AndresRicoM/MAIA/images/light_module.png

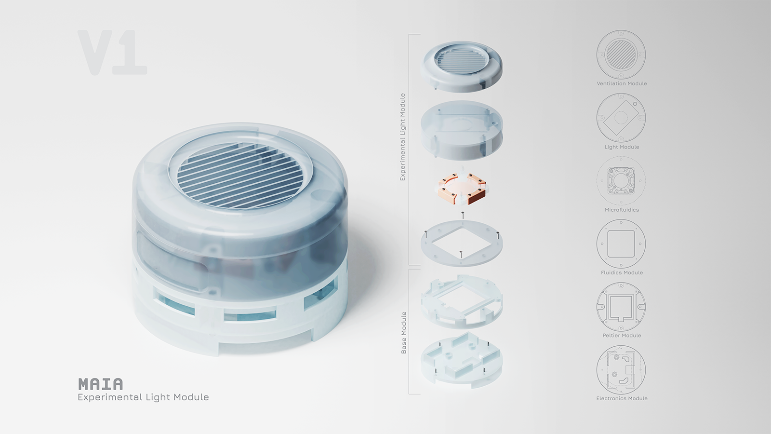
images/light_module.png
