AndresRicoM/MAIA/images/MAIA.gif

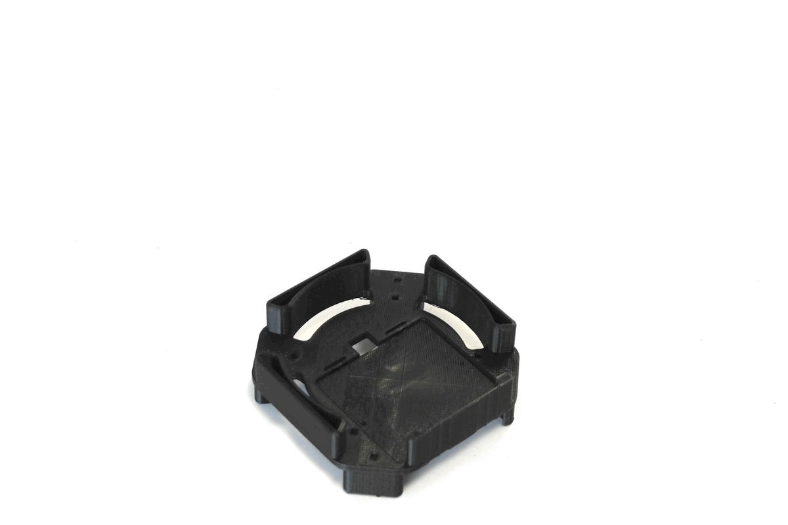
images/MAIA.gif
