AndresRicoM/MAIA/images/reactor.jpeg

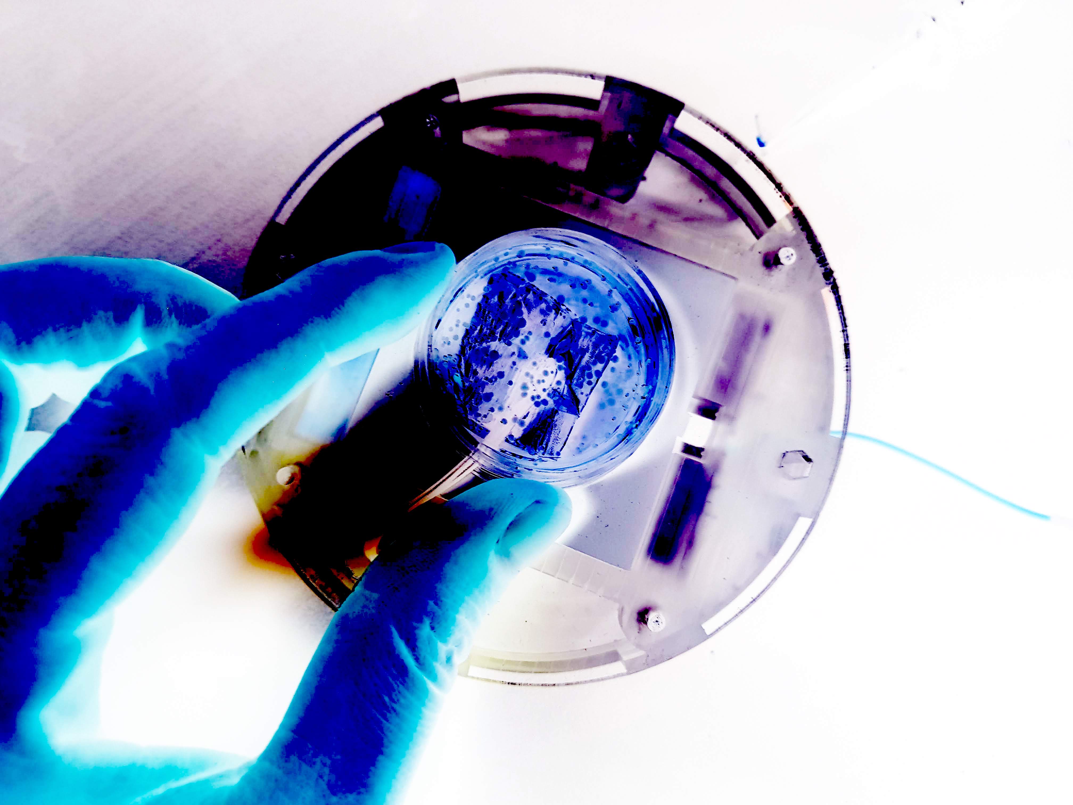
images/reactor.jpeg
