AndresRicoM/MAIA/simple_power_module/milling_files/maia_simple_power_traces.png

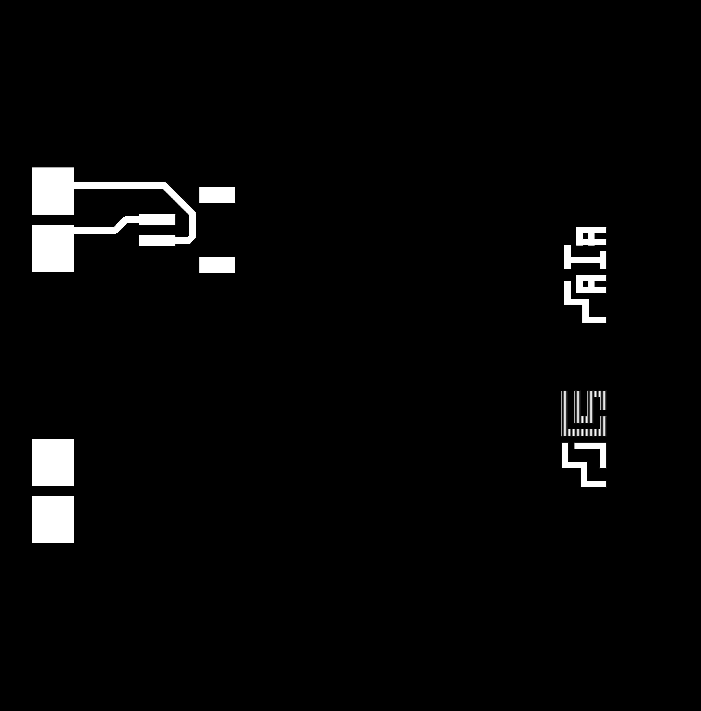
simple_power_module/milling_files/maia_simple_power_traces.png
