AndresRicoM/MAIA/light_module/pcb_fabrication/milling_files/maia_light_outline_out.png

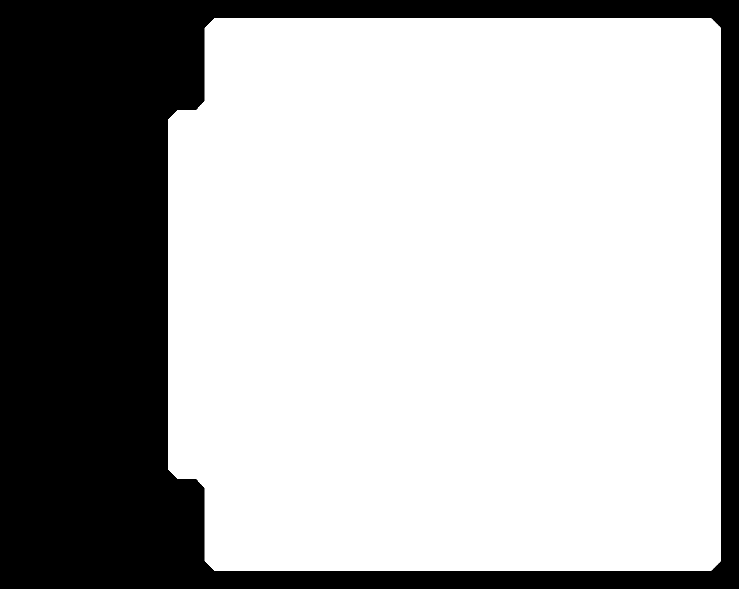
light_module/pcb_fabrication/milling_files/maia_light_outline_out.png
