AndresRicoM/MAIA/light_module/pcb_fabrication/milling_files/maia_light_traces.png

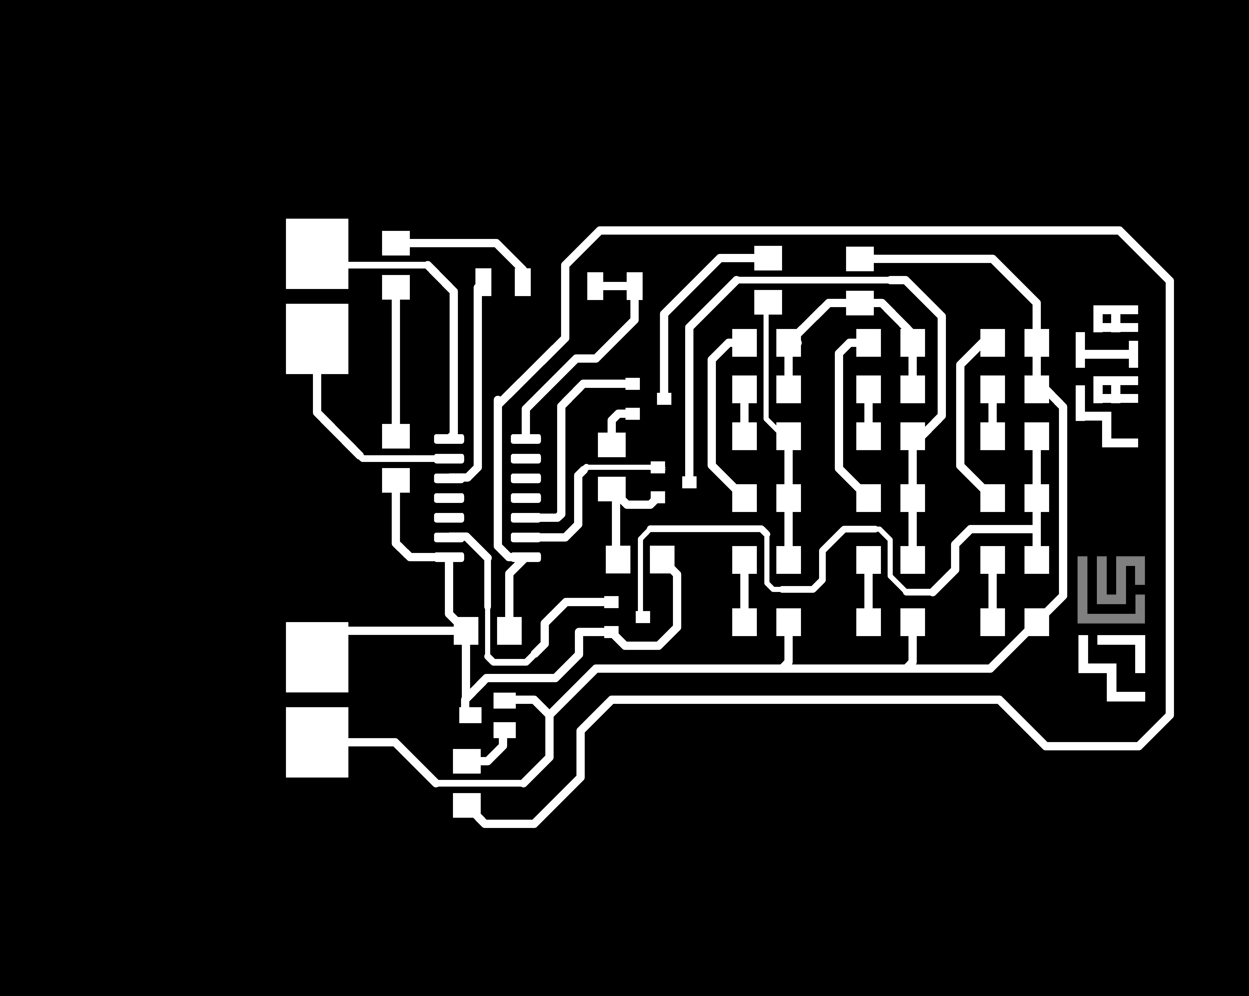
light_module/pcb_fabrication/milling_files/maia_light_traces.png
