AndresRicoM/MAIA/mother_module/pcb_fabrication/milling_files/mother_board_outline_in.png

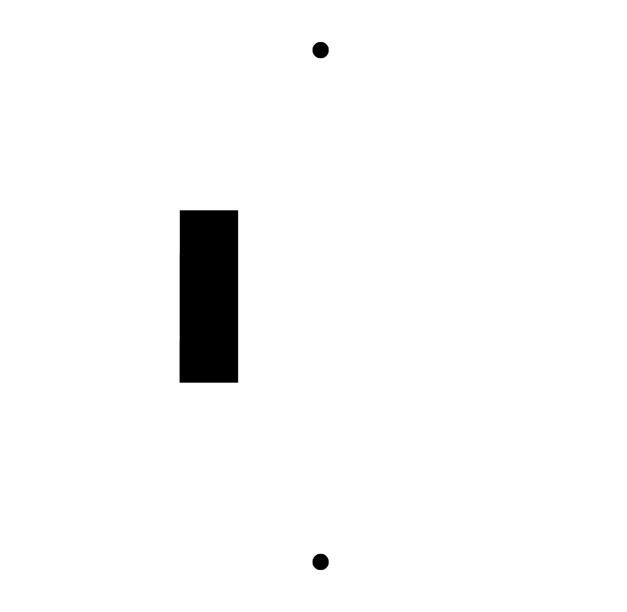
mother_module/pcb_fabrication/milling_files/mother_board_outline_in.png
