AndresRicoM/MAIA/mother_module/pcb_fabrication/milling_files/mother_board_traces.png

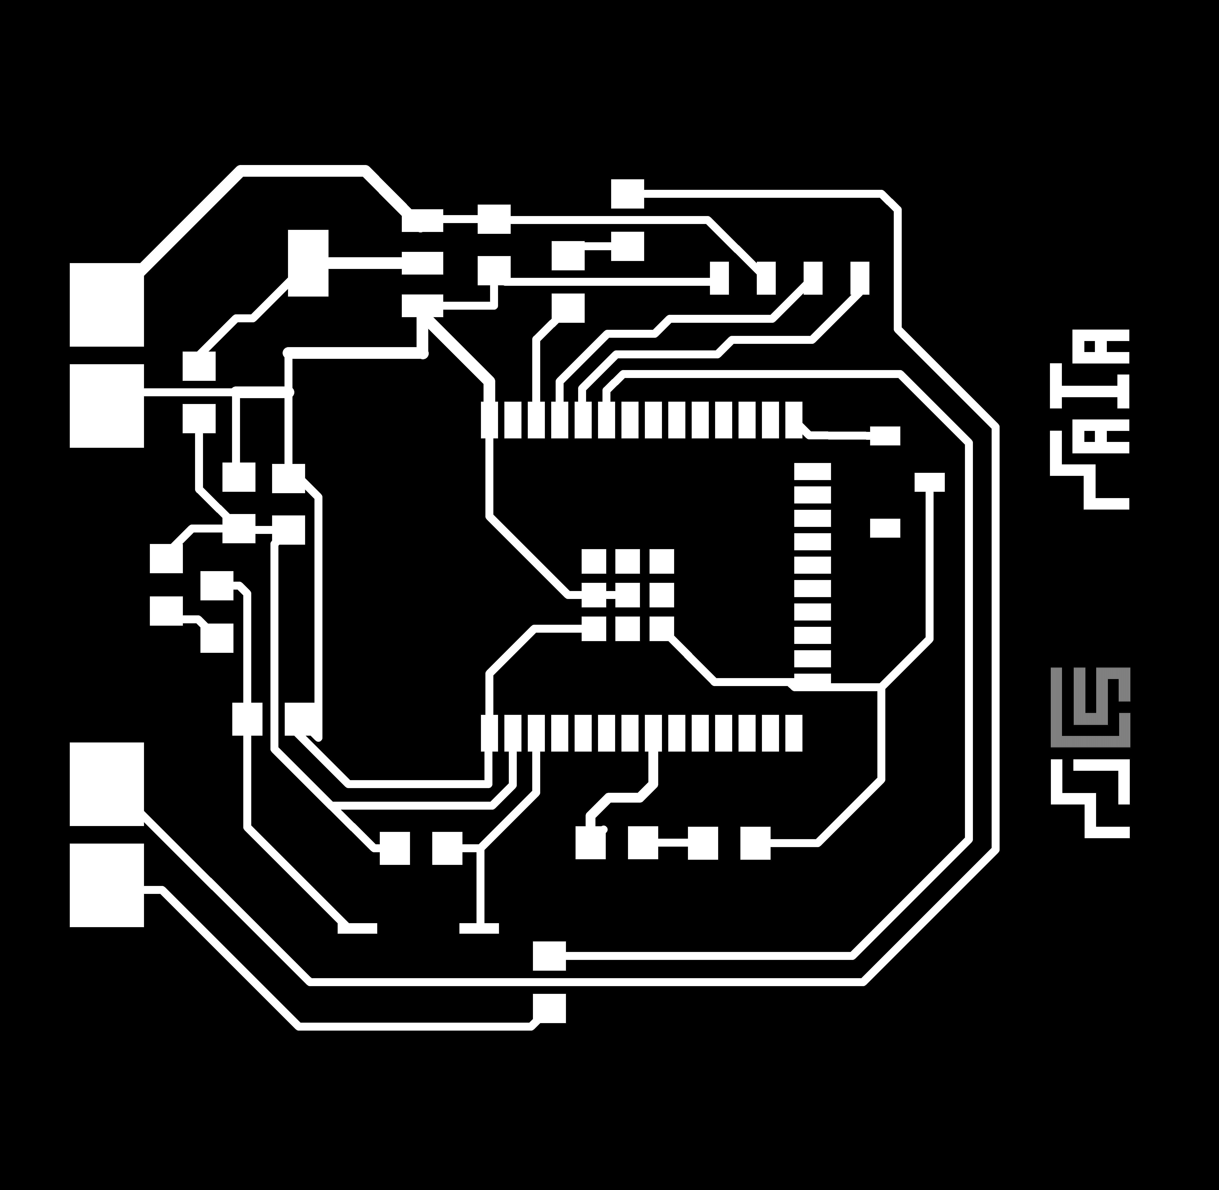
mother_module/pcb_fabrication/milling_files/mother_board_traces.png
