AndresRicoM/MAIA/temperature_module/pcb_fabrication/milling_files/maia_temperature_traces.png

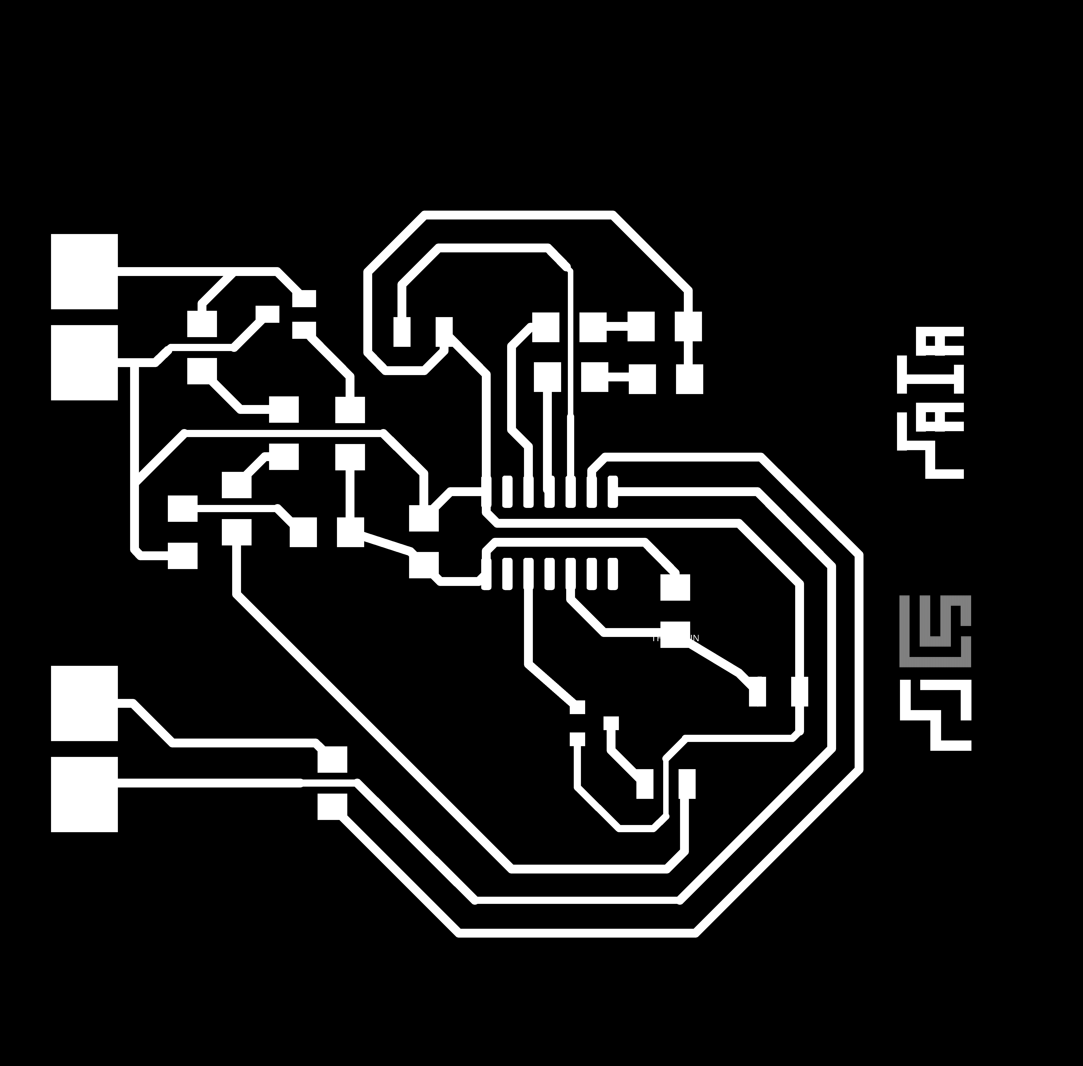
temperature_module/pcb_fabrication/milling_files/maia_temperature_traces.png
